cristianoag/trh9000/Images/2022-08-10_23-06.png

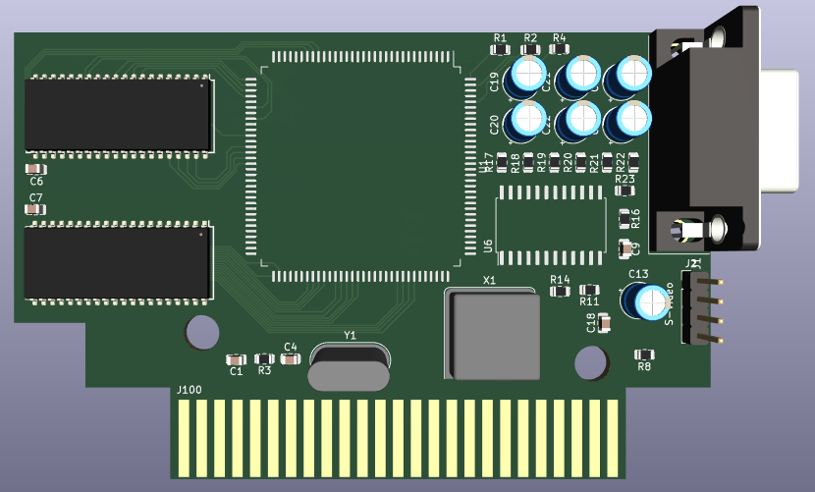
Images/2022-08-10_23-06.png
