cristianoag/trh9000/Images/2022-08-20_22-34.png

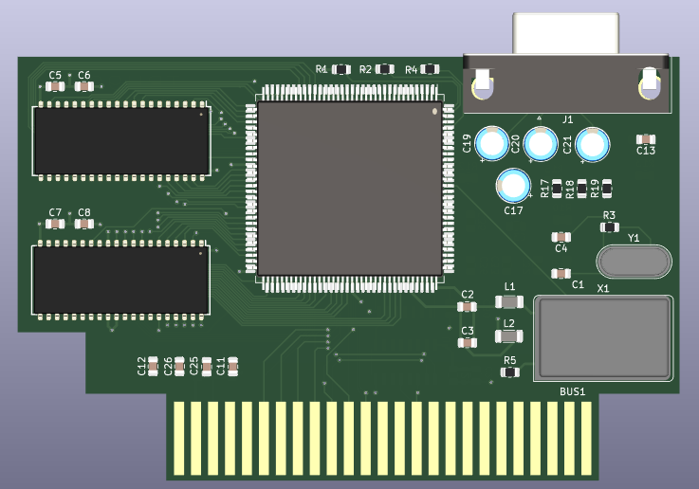
Images/2022-08-20_22-34.png
