cristianoag/trh9000/Images/2022-08-21_16-16.png

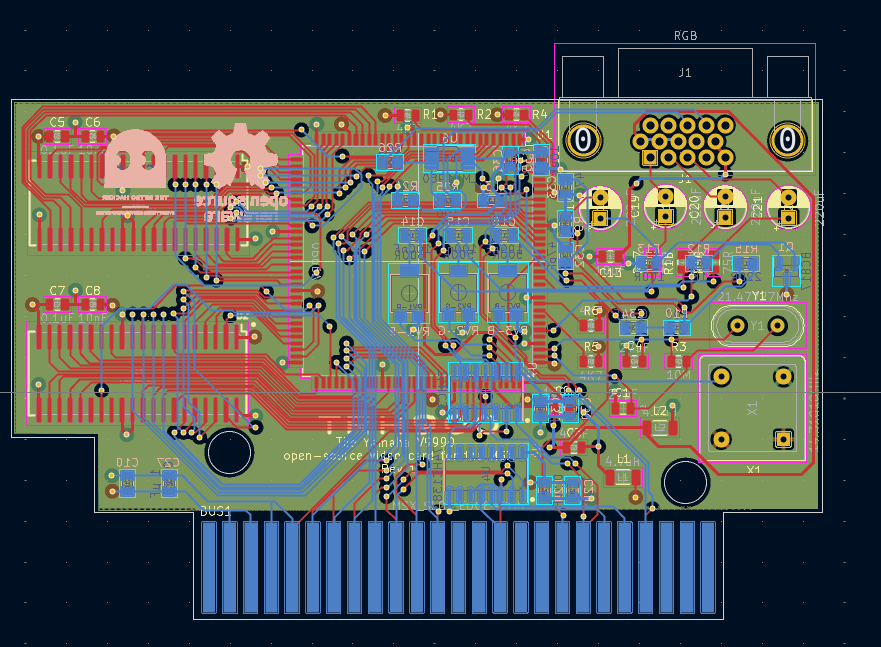
Images/2022-08-21_16-16.png
