cristianoag/trh9000/Images/2022-08-21_16-17.png

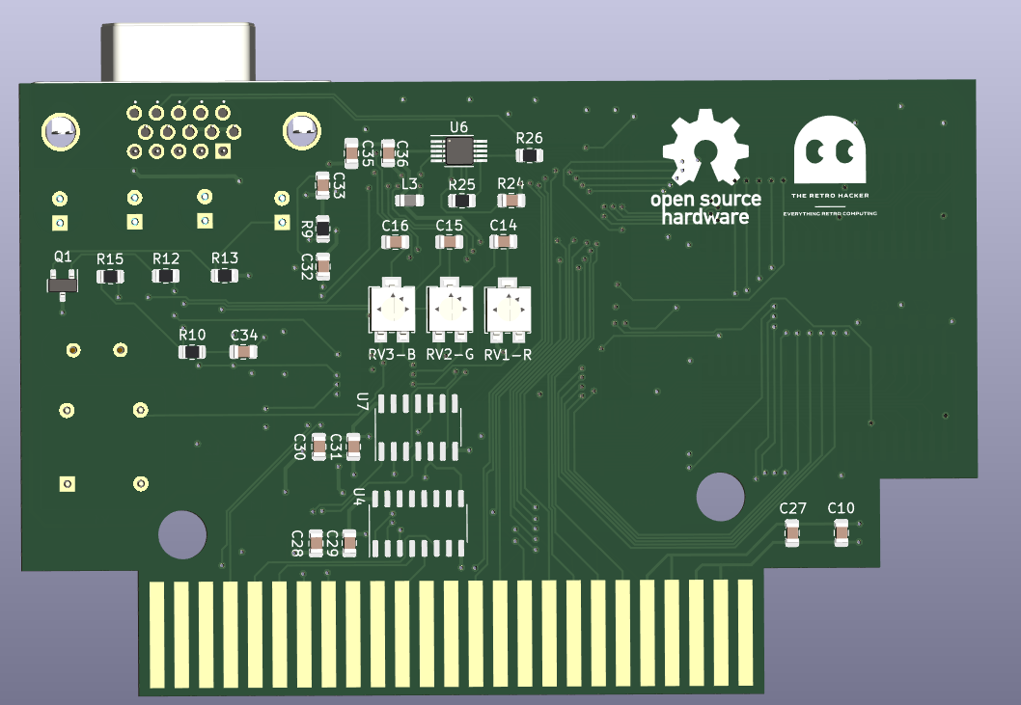
Images/2022-08-21_16-17.png
