cristianoag/trh9000/Images/2022-10-03_20-58_1.jpg

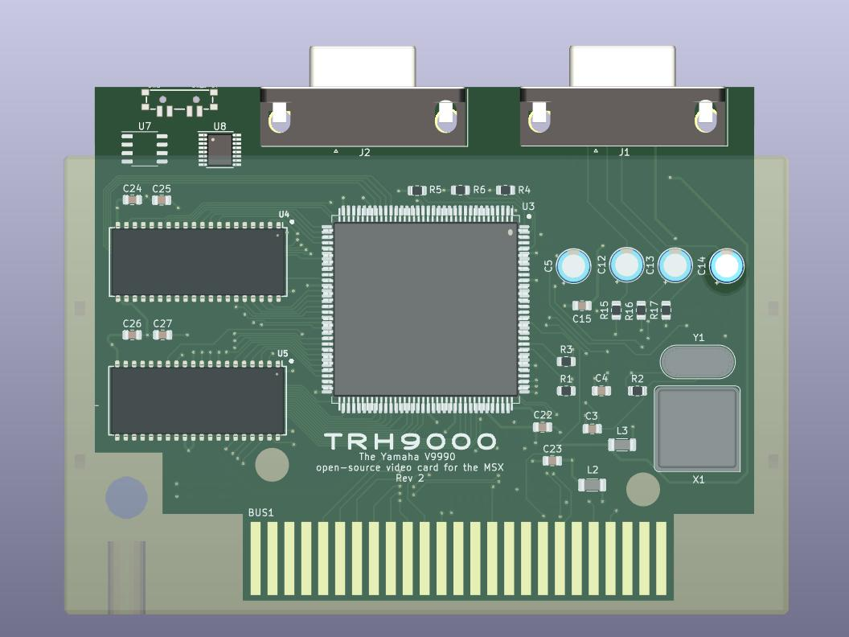
Images/2022-10-03_20-58_1.jpg
