cristianoag/trh9000/Images/2022-10-31_21-31.png

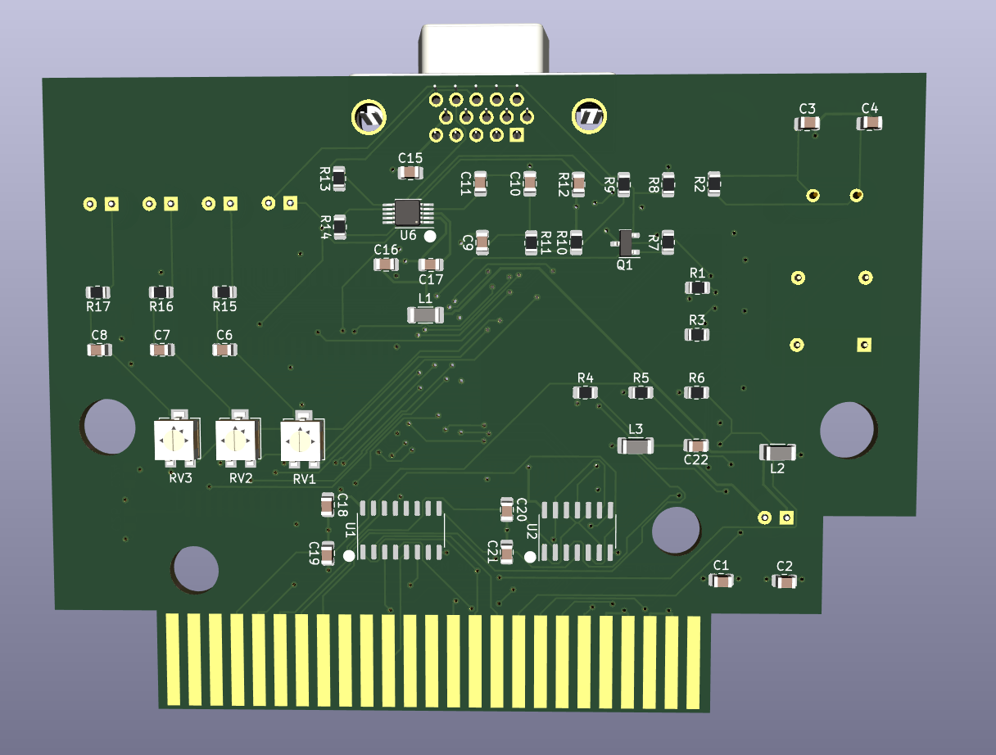
Images/2022-10-31_21-31.png
