cristianoag/trh9000/Images/2022-11-27_00-35.jpg

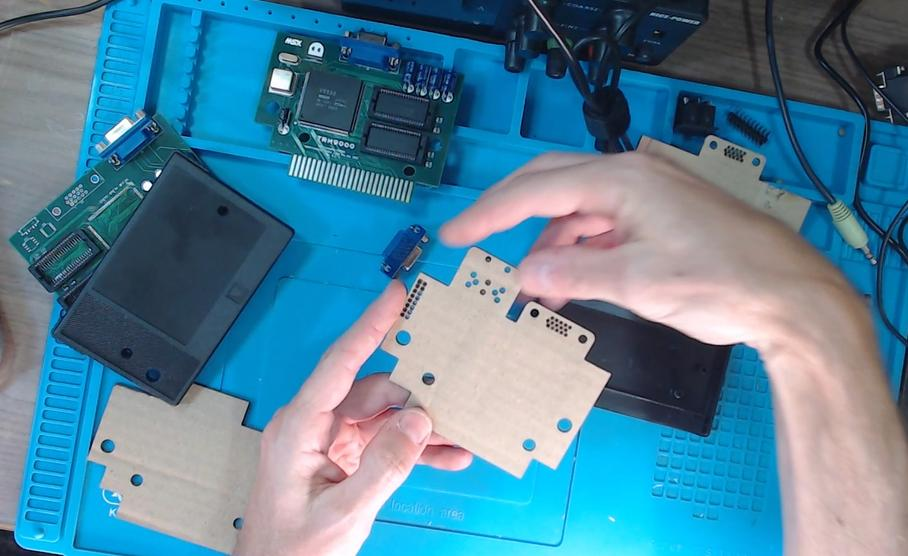
Images/2022-11-27_00-35.jpg
