cristianoag/trh9000/Images/2022-11-27_00-36.jpg

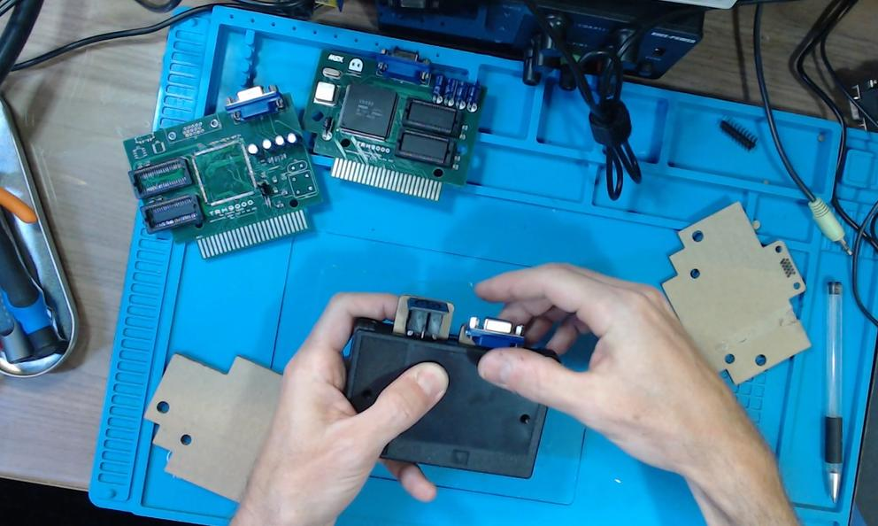
Images/2022-11-27_00-36.jpg
