cristianoag/trh9000/Images/2022-11-27_01-49.jpg

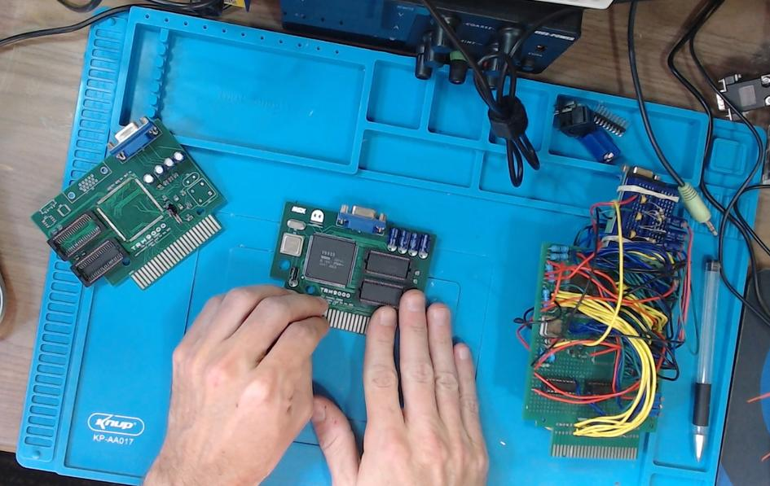
Images/2022-11-27_01-49.jpg
