cristianoag/trh9000/Images/2023-09-24_18-45.png

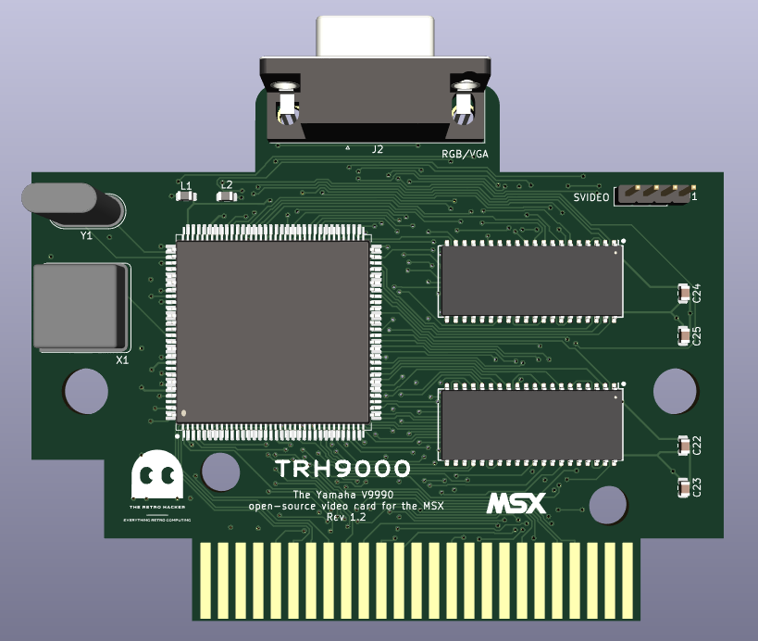
Images/2023-09-24_18-45.png
