cristianoag/trh9000/Images/2024-02-22_14-27_1.png

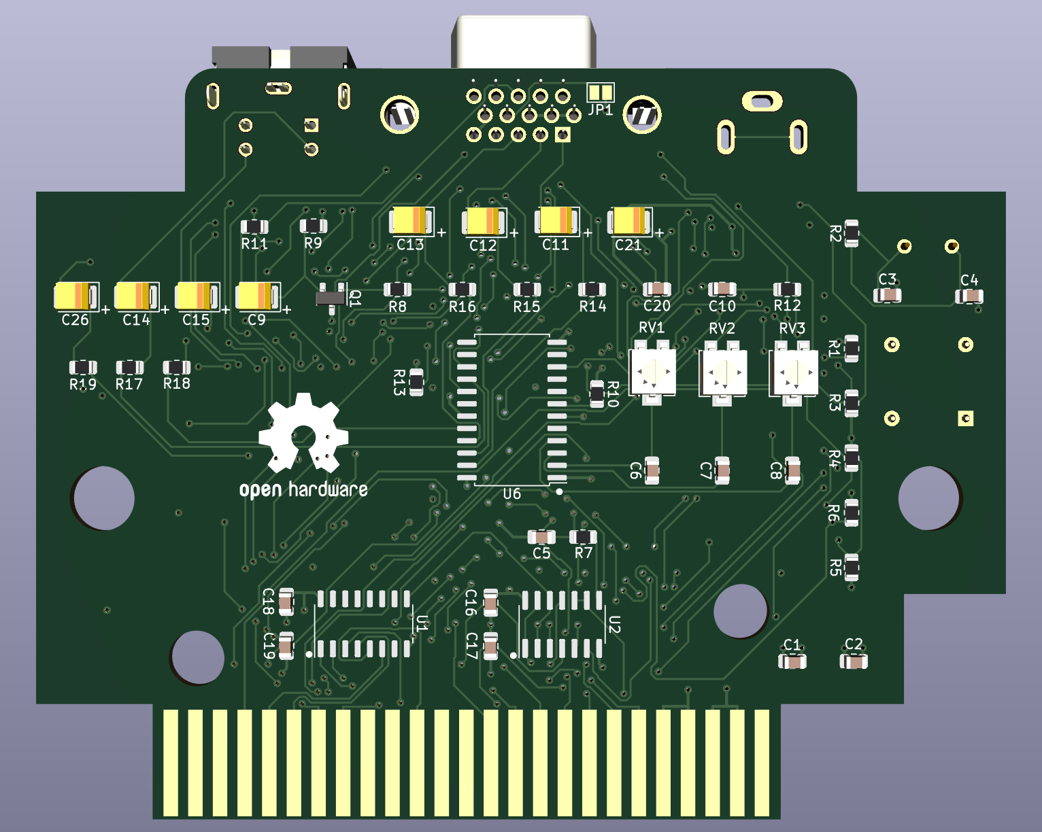
Images/2024-02-22_14-27_1.png
