cristianoag/trh9000/Images/20221031_005830422_iOS_sm.jpg

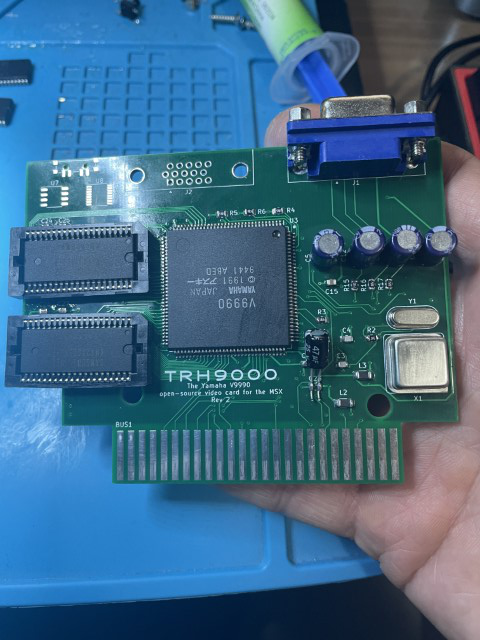
Images/20221031_005830422_iOS_sm.jpg
