cristianoag/trh9000/Images/20221031_005840287_iOS_sm.jpg

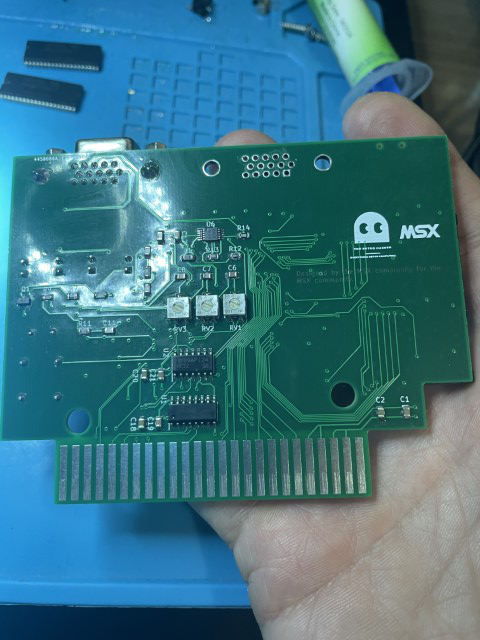
Images/20221031_005840287_iOS_sm.jpg
