cristianoag/trh9000/Images/20221127_033056656_iOS.jpg

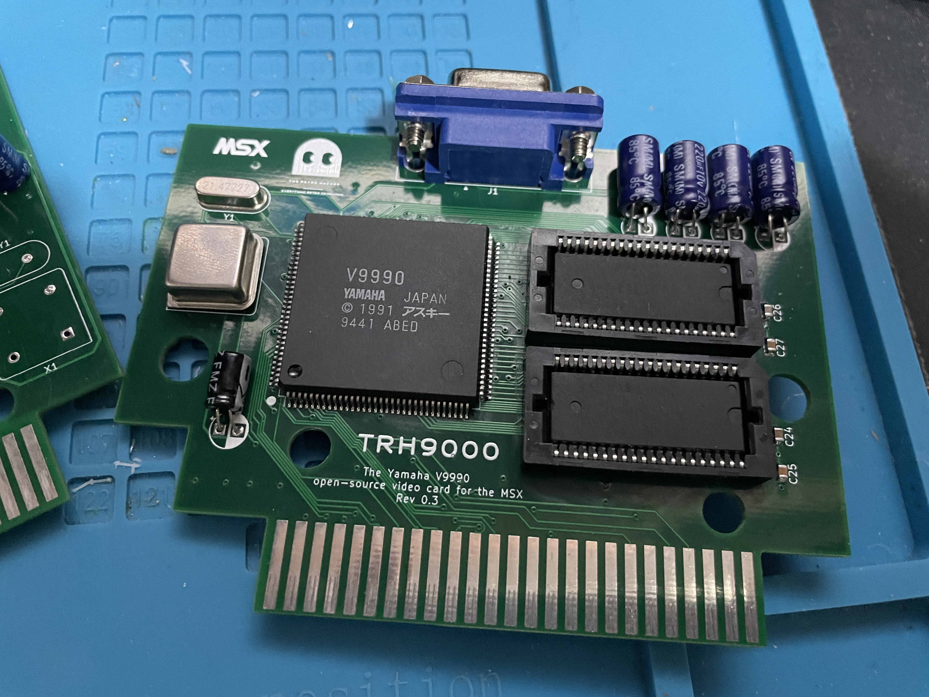
Images/20221127_033056656_iOS.jpg
