cristianoag/trh9000/Images/20221127_033313406_iOS.jpg

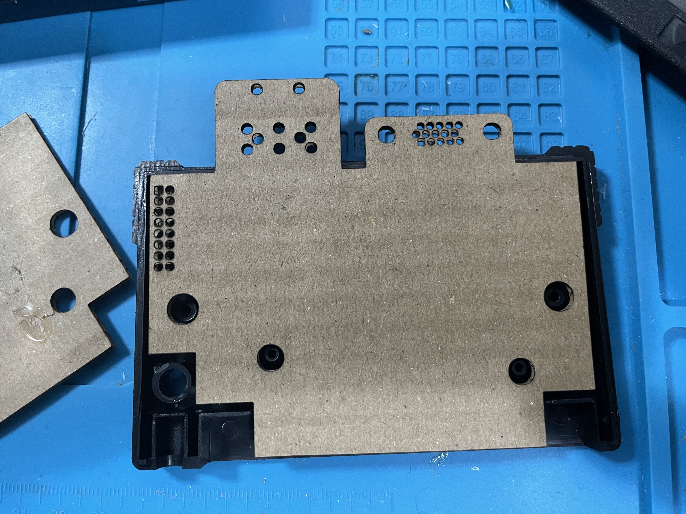
Images/20221127_033313406_iOS.jpg
