cristianoag/trh9000/Images/20221127_033321807_iOS.jpg

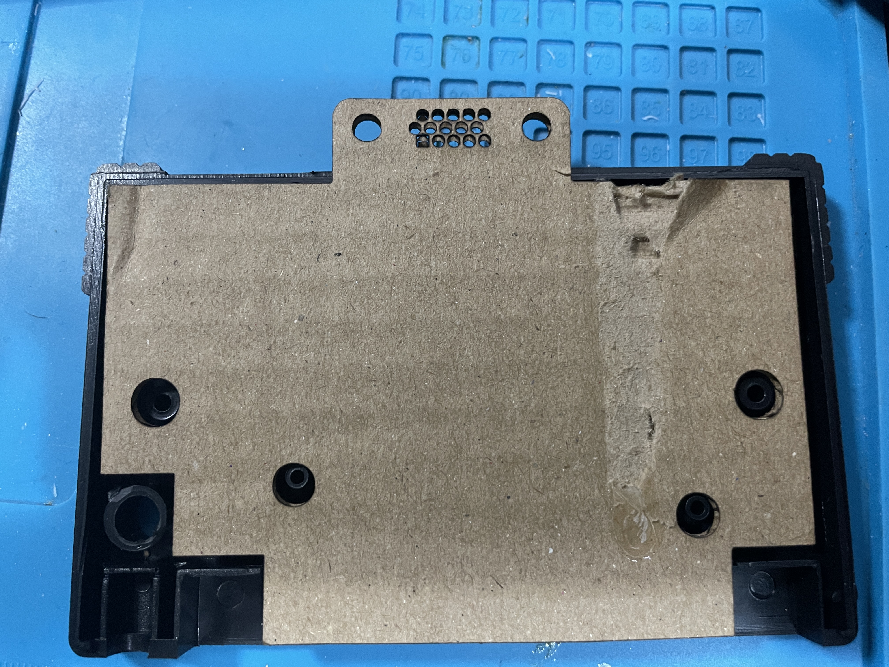
Images/20221127_033321807_iOS.jpg
