cristianoag/trh9000/Images/20230324_005049625_iOS.jpg

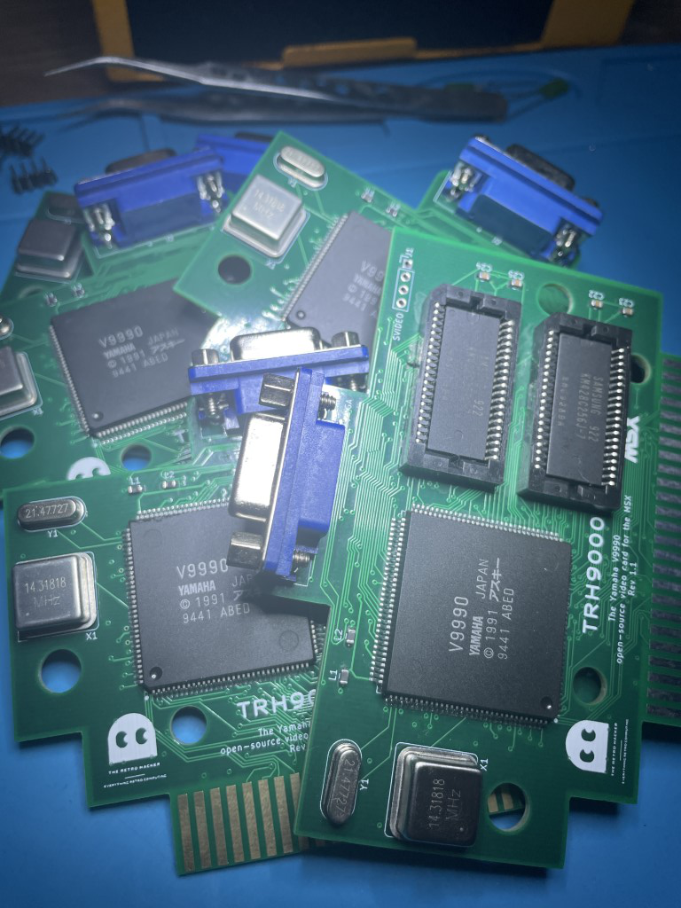
Images/20230324_005049625_iOS.jpg
