cristianoag/trh9000/Images/Screenshot 2022-12-25 18-41-01.png

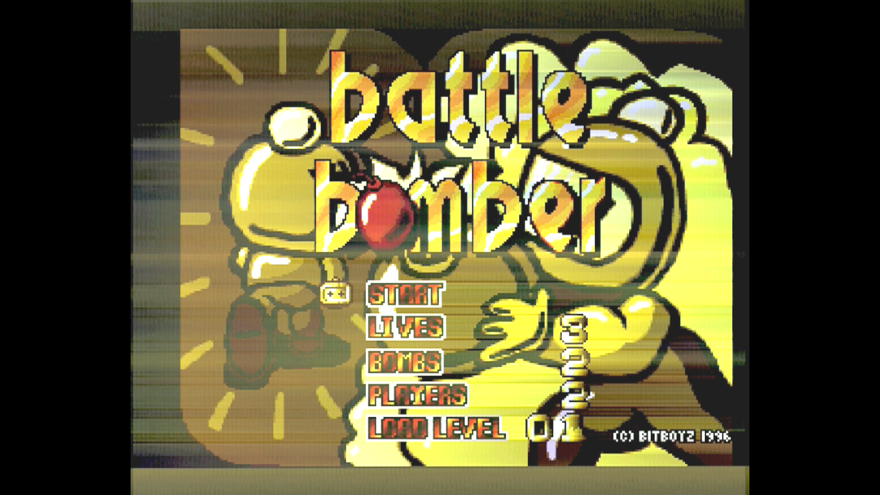
Images/Screenshot 2022-12-25 18-41-01.png
