cristianoag/trh9000/Images/SVIDEO2.jpg

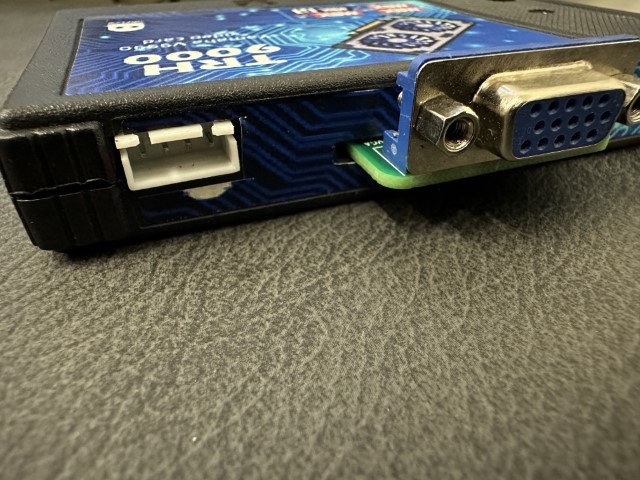
Images/SVIDEO2.jpg
