cristianoag/trh9000/Images/SVIDEO3.png

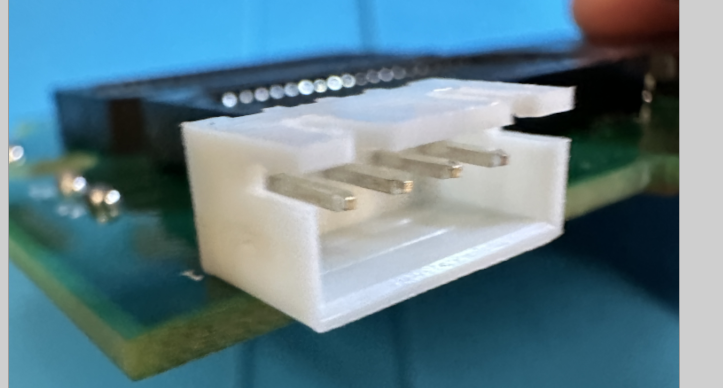
Images/SVIDEO3.png
