cristianoag/trh9000/Images/TRH9000.jpg

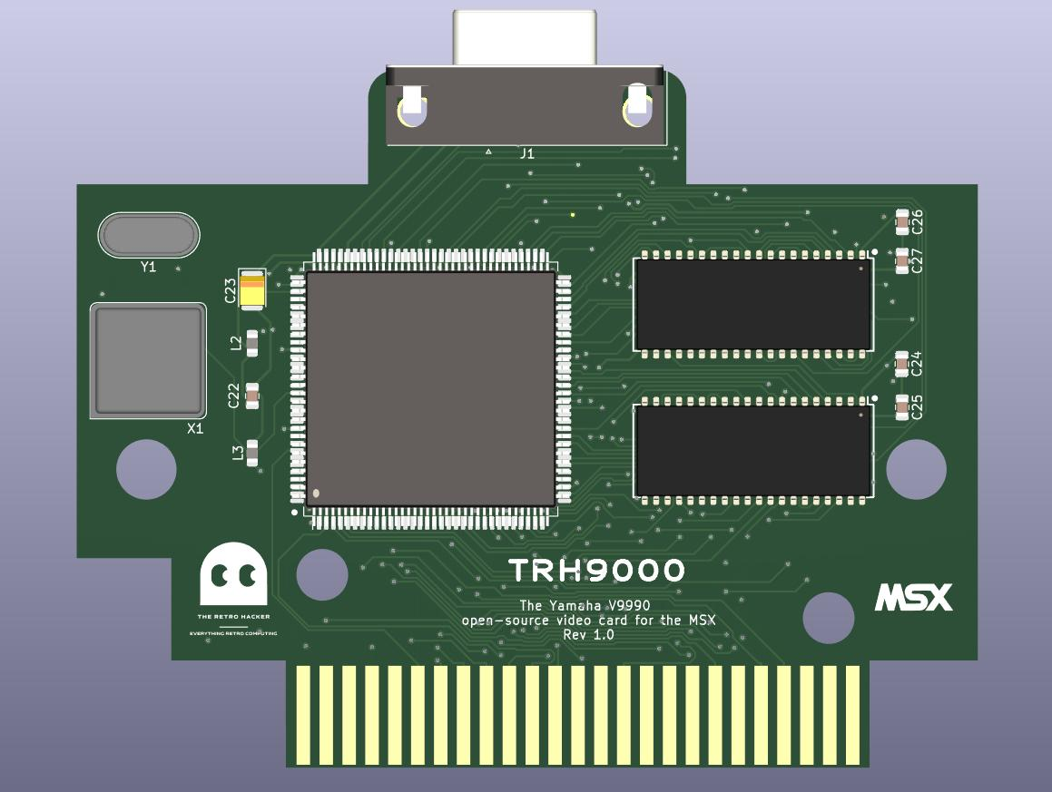
Images/TRH9000.jpg
