cristianoag/trh9000/Images/20220921_051811503_iOS.jpg

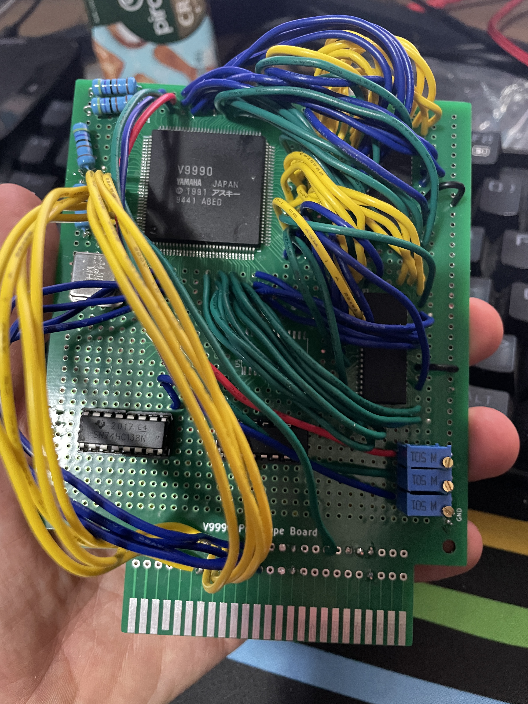
Images/20220921_051811503_iOS.jpg
