cristianoag/trh9000/Images/20221002_005516778_iOS.jpg

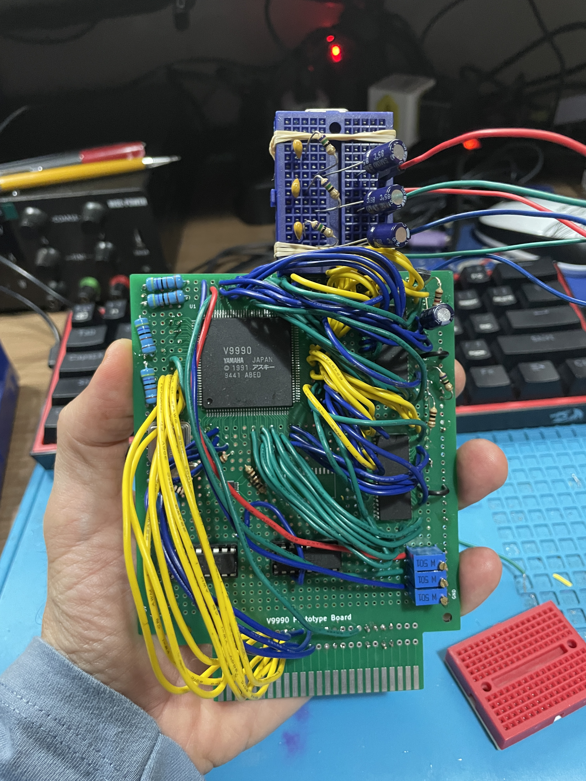
Images/20221002_005516778_iOS.jpg
