cristianoag/trh9000/Images/20221003_193700999_iOS.jpg

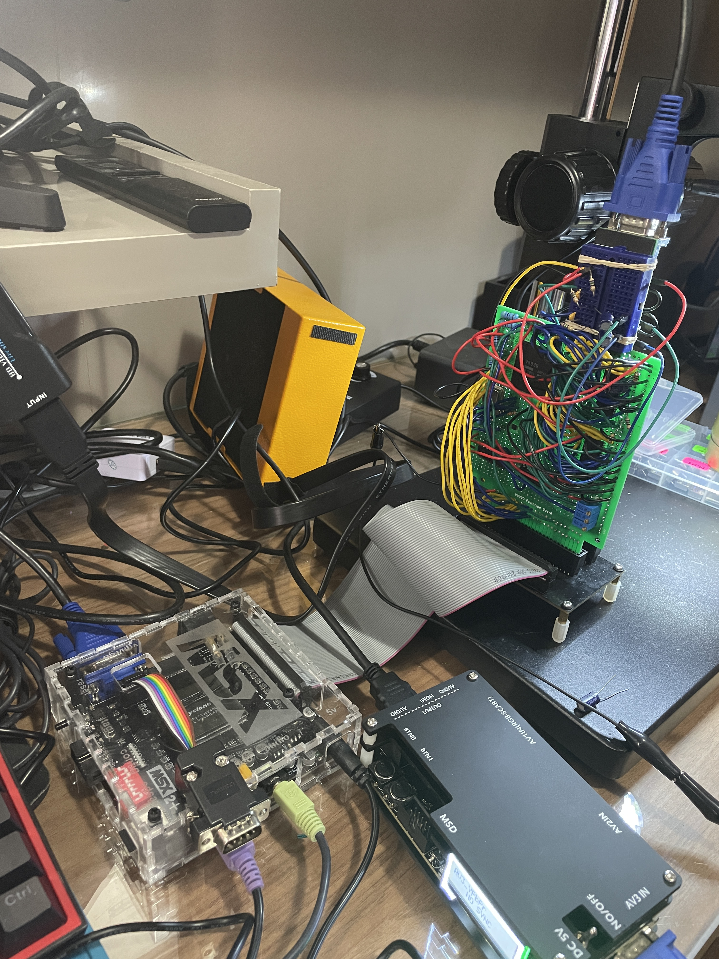
Images/20221003_193700999_iOS.jpg
